hunterchev/computer-enclosure/renders/front_inside.png

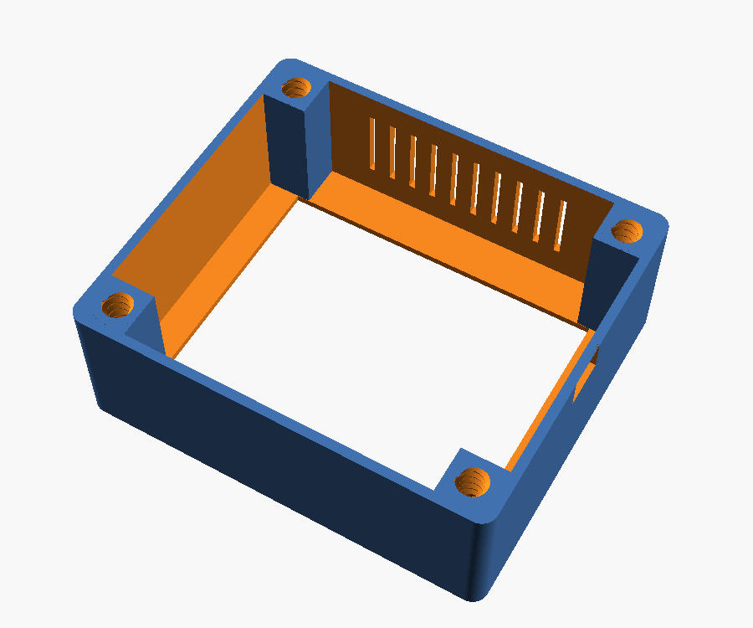
renders/front_inside.png
