hunterchev/computer-enclosure/renders/assembly_back.png

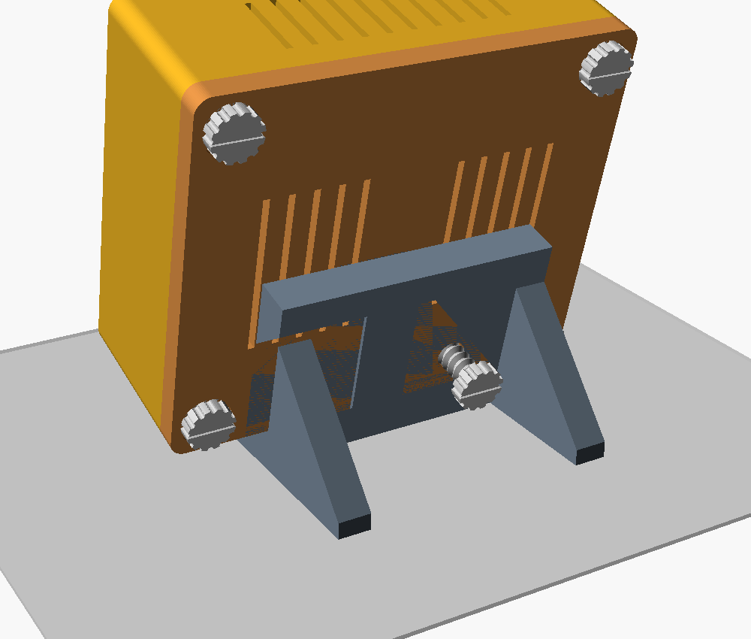
renders/assembly_back.png
