hunterchev/computer-enclosure/renders/assembly_iso.png

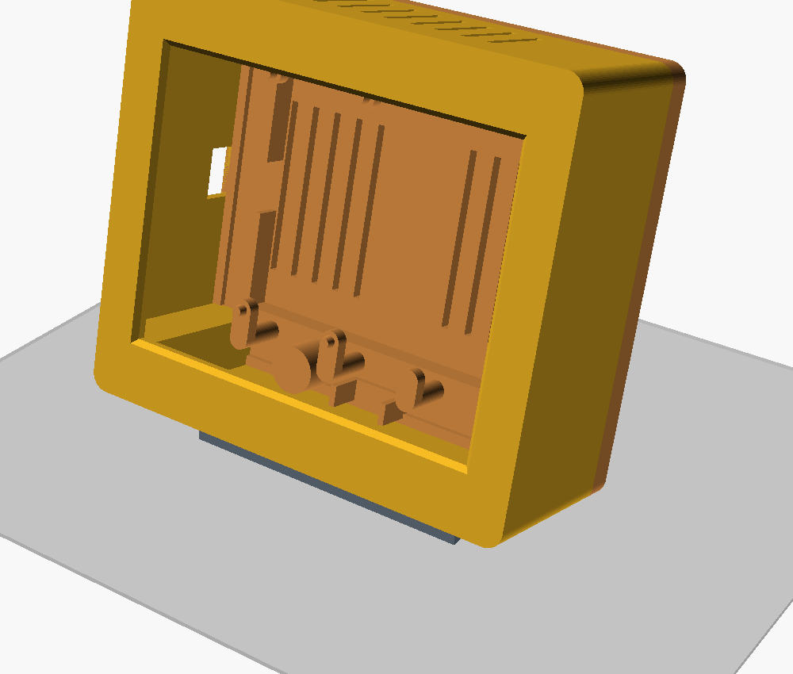
renders/assembly_iso.png
