hunterchev/computer-enclosure/renders/assembly_side.png

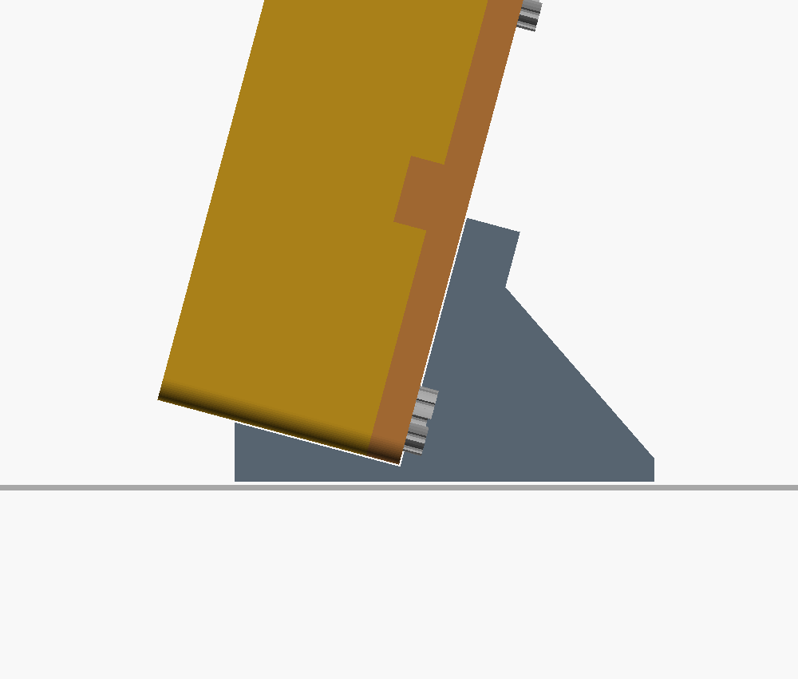
renders/assembly_side.png
