hunterchev/computer-enclosure/renders/assembly_upright_back.png

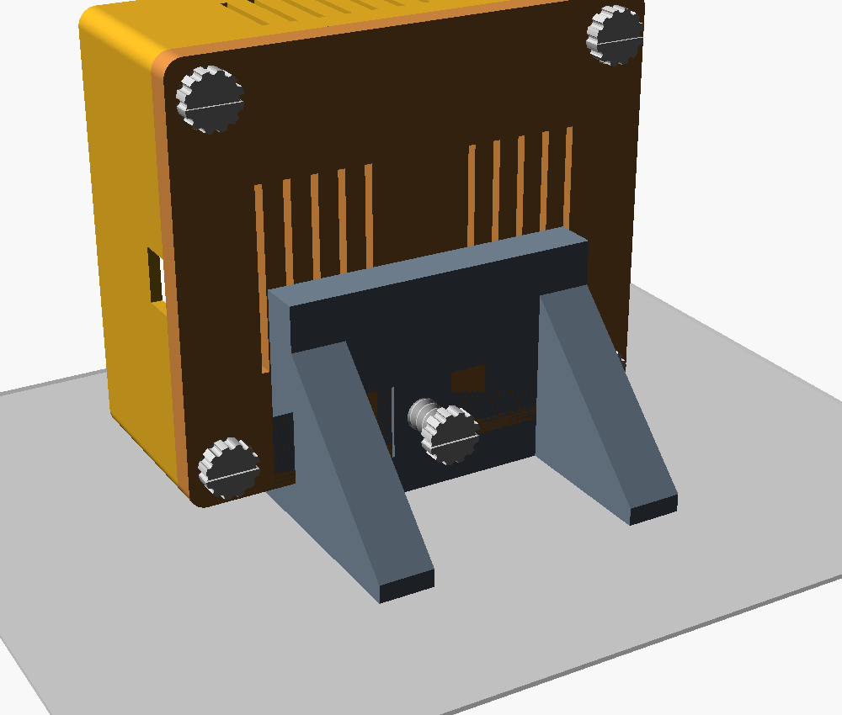
renders/assembly_upright_back.png
