hunterchev/computer-enclosure/renders/assembly_upright_side.png

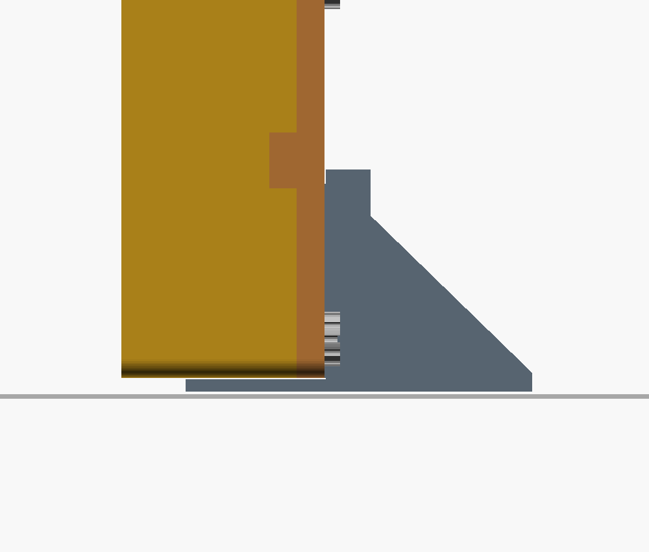
renders/assembly_upright_side.png
