hunterchev/computer-enclosure/renders/stand_print.png

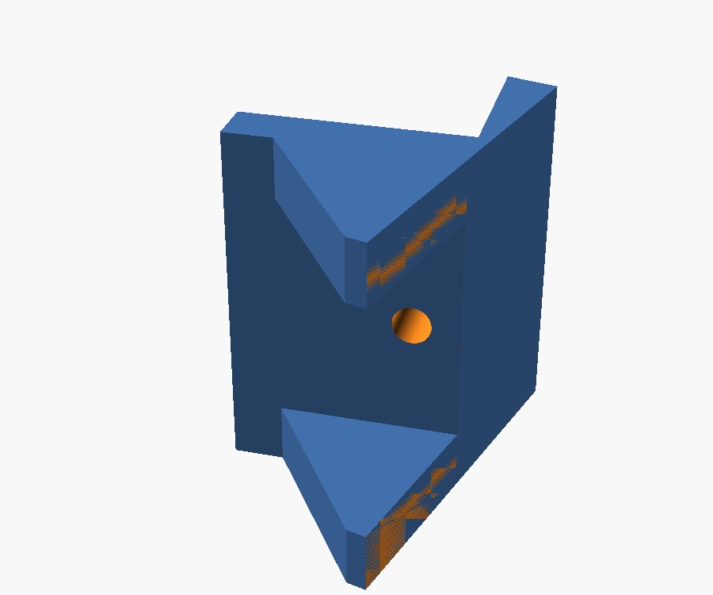
renders/stand_print.png
